YCAMInterlab/MOTIONER/documents/ai/IMU diagram.png

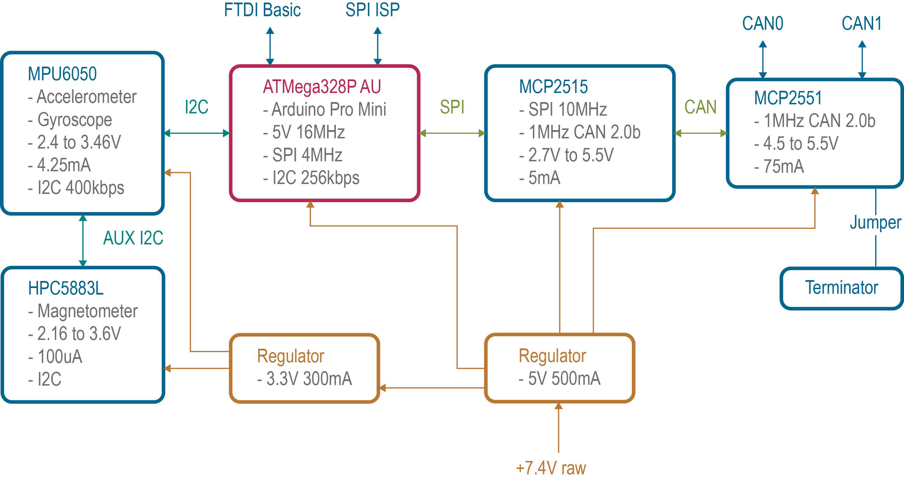
documents/ai/IMU diagram.png
