YCAMInterlab/MOTIONER/oF/MOTIONER/bin/data/images/L.png

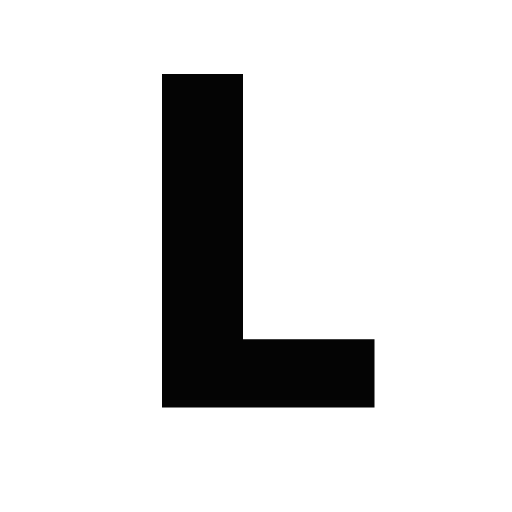
oF/MOTIONER/bin/data/images/L.png
