YCAMInterlab/MOTIONER/oF/MOTIONER/bin/data/images/R.png

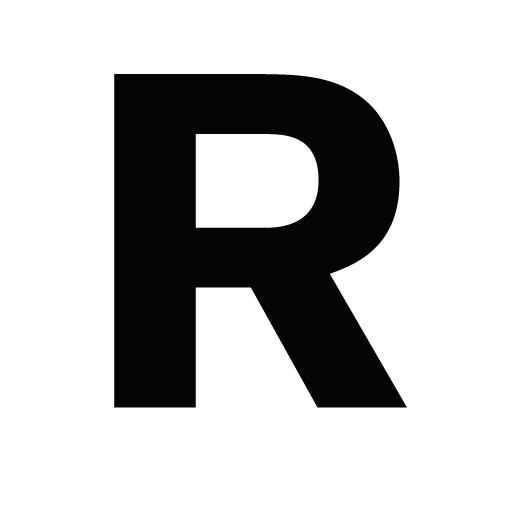
oF/MOTIONER/bin/data/images/R.png
